Dieu-de-l-elec/AngstromIO-devboard/IMG/AIO demo.gif

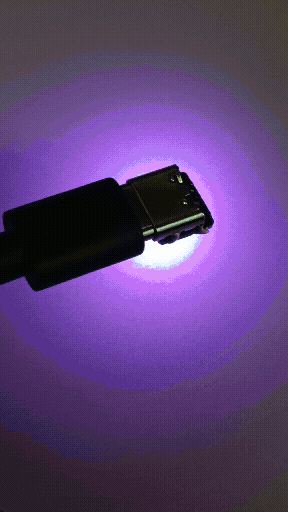
IMG/AIO demo.gif
