Dieu-de-l-elec/AngstromIO-devboard/IMG/angstromIO 3d S1.png

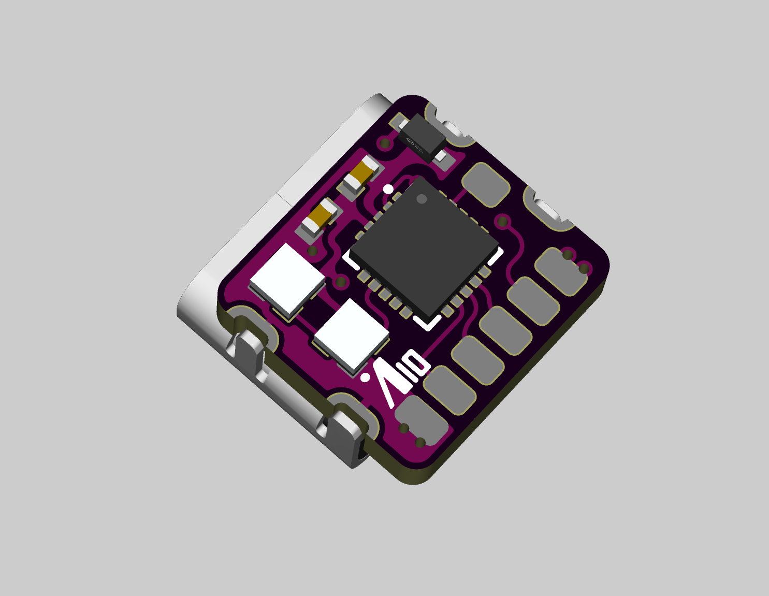
IMG/angstromIO 3d S1.png
