Dieu-de-l-elec/AngstromIO-devboard/IMG/angstromIO 3d S2.png

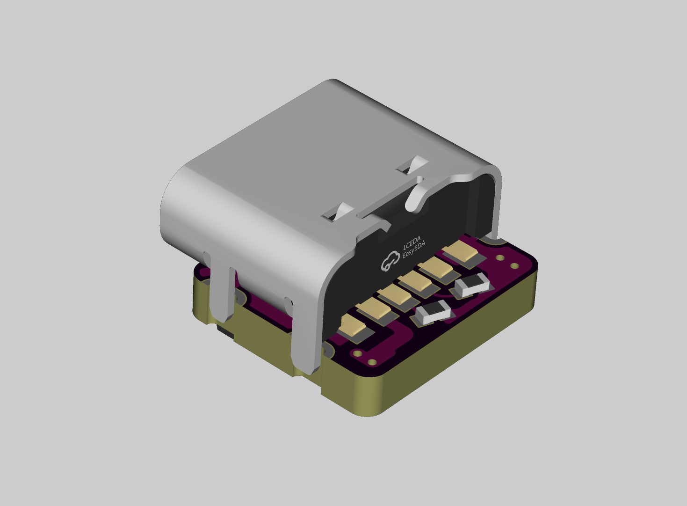
IMG/angstromIO 3d S2.png
