Dieu-de-l-elec/AngstromIO-devboard/IMG/angstromIO 3d S3.png

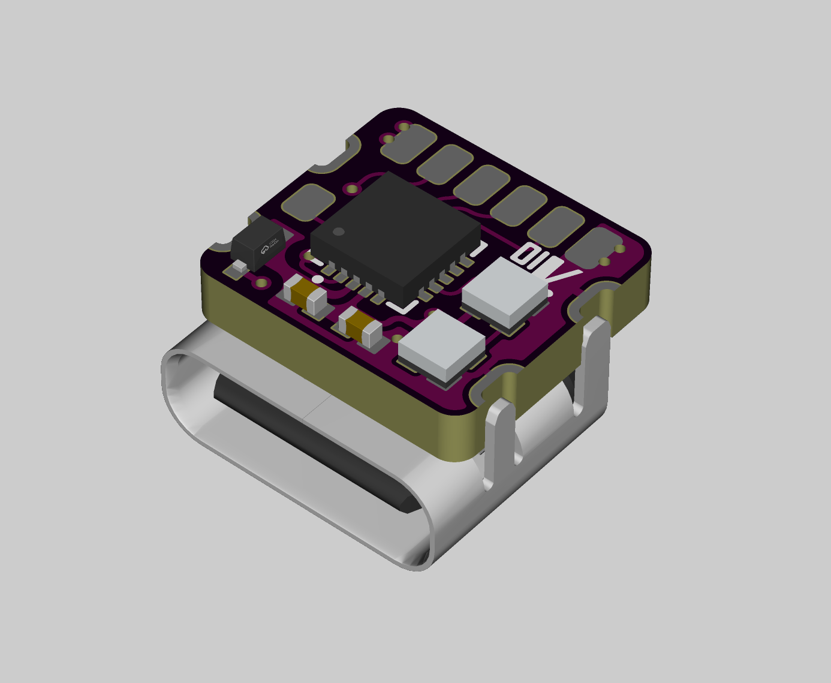
IMG/angstromIO 3d S3.png
