Dieu-de-l-elec/AngstromIO-devboard/IMG/angstromIO 3d S4.png

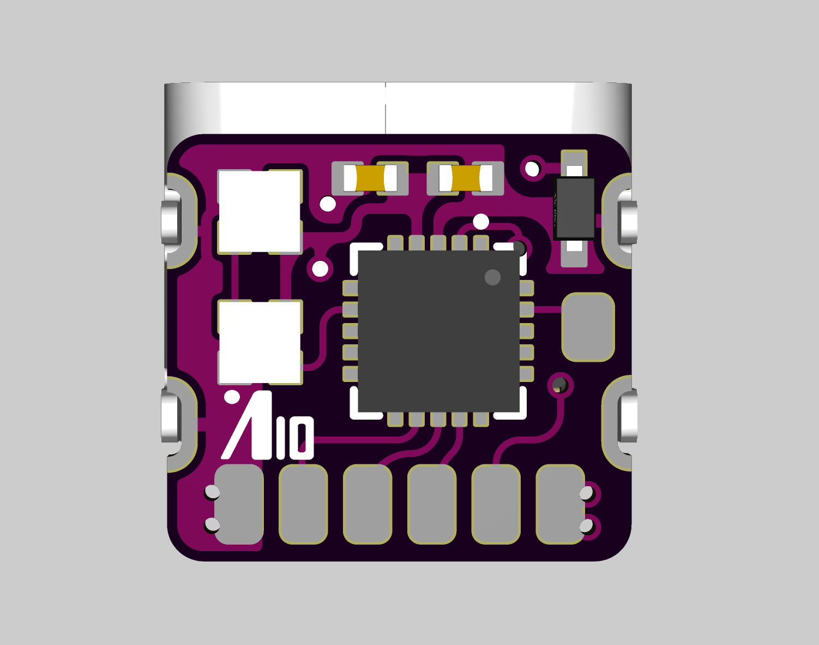
IMG/angstromIO 3d S4.png
