Dieu-de-l-elec/AngstromIO-devboard/IMG/angstromIO 3d S5.png

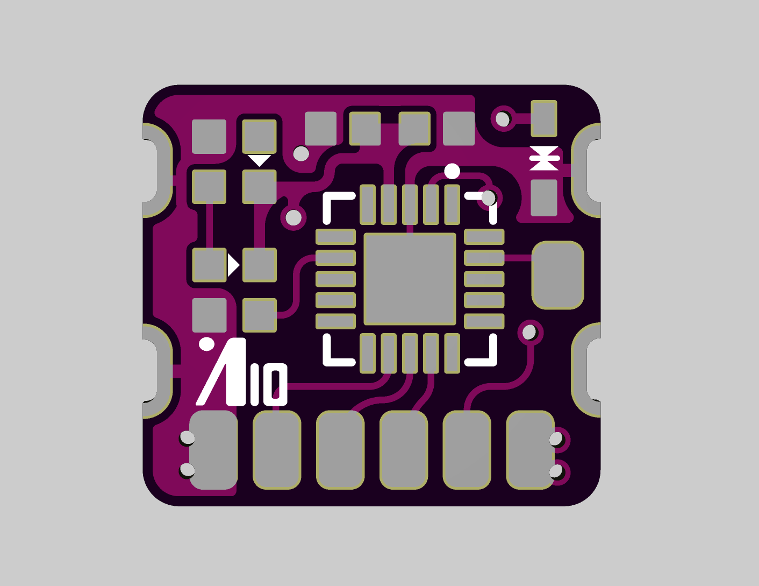
IMG/angstromIO 3d S5.png
