Dieu-de-l-elec/AngstromIO-devboard/IMG/angstromIO 3d S6.png

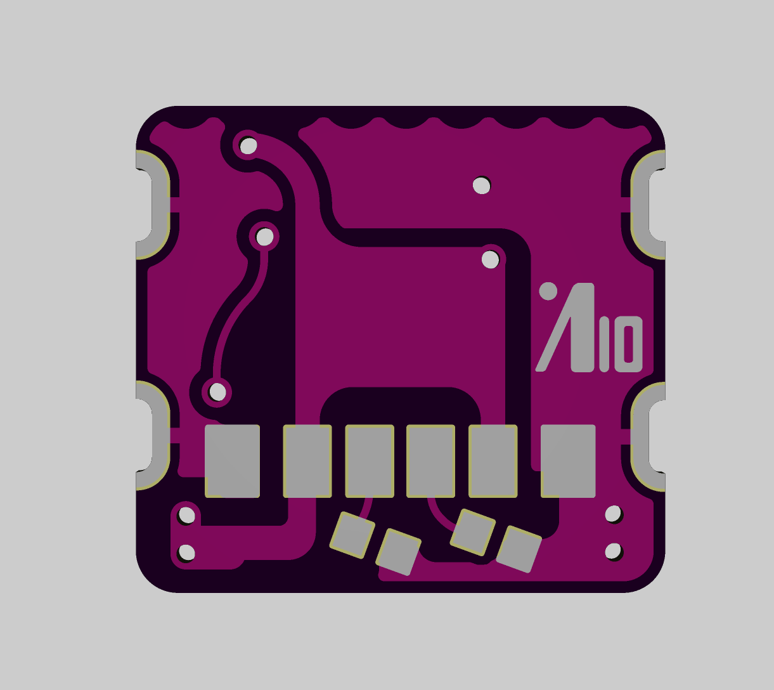
IMG/angstromIO 3d S6.png
