Dieu-de-l-elec/AngstromIO-devboard/IMG/CH32 Devboard 3D.png

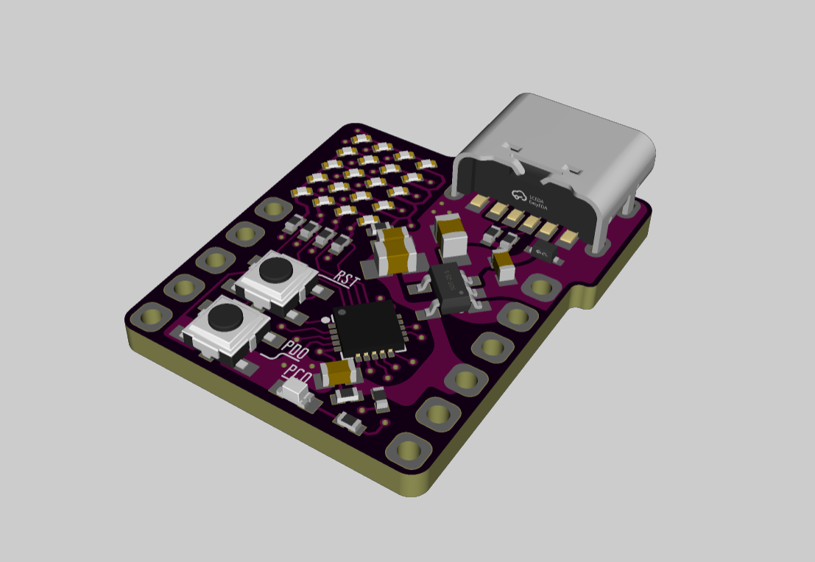
IMG/CH32 Devboard 3D.png
