Dieu-de-l-elec/AngstromIO-devboard/IMG/CH32 Devboard btm.png

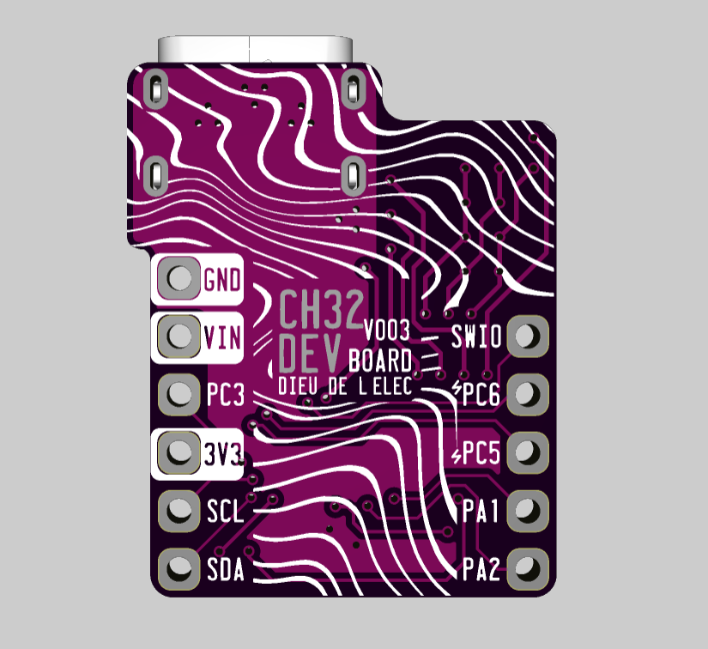
IMG/CH32 Devboard btm.png
