Dieu-de-l-elec/AngstromIO-devboard/IMG/CH32 Devboard top.png

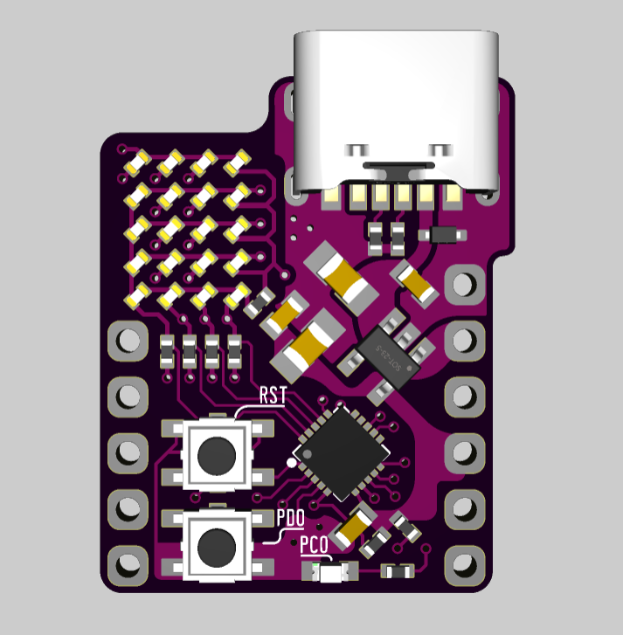
IMG/CH32 Devboard top.png
