Dieu-de-l-elec/AngstromIO-devboard/IMG/Global.jpg

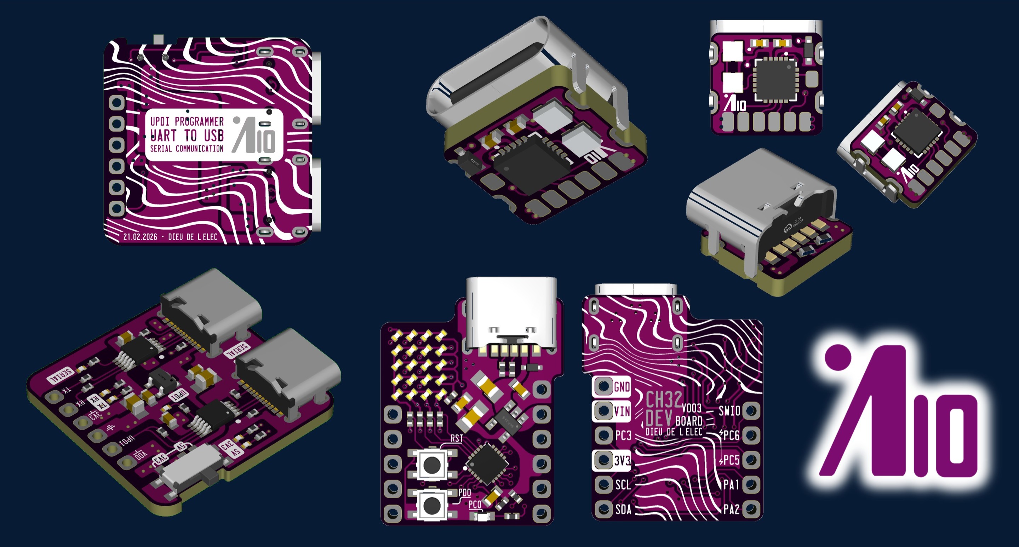
IMG/Global.jpg
