Dieu-de-l-elec/AngstromIO-devboard/IMG/Layout bottom AIO clean.png

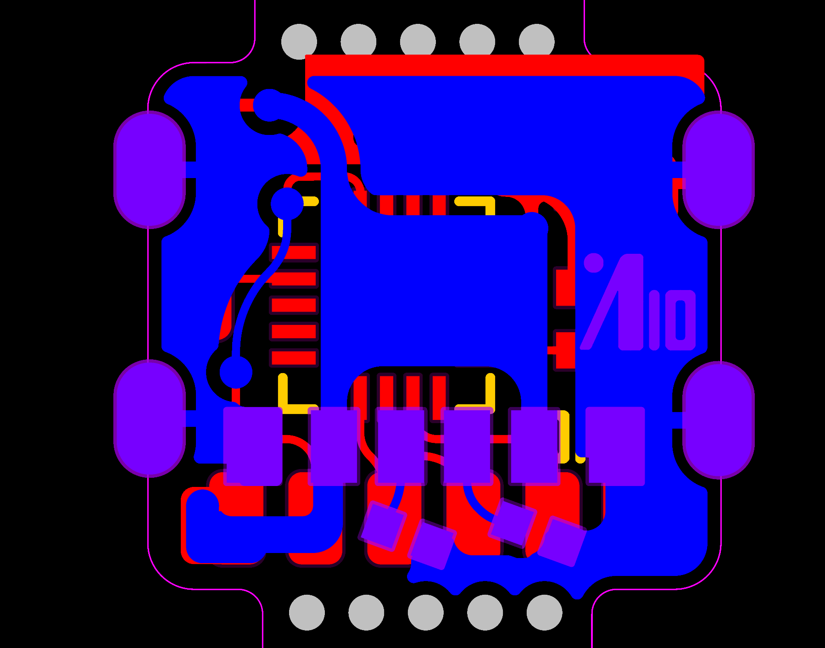
IMG/Layout bottom AIO clean.png
