Dieu-de-l-elec/AngstromIO-devboard/IMG/Layout bottom AIO.png

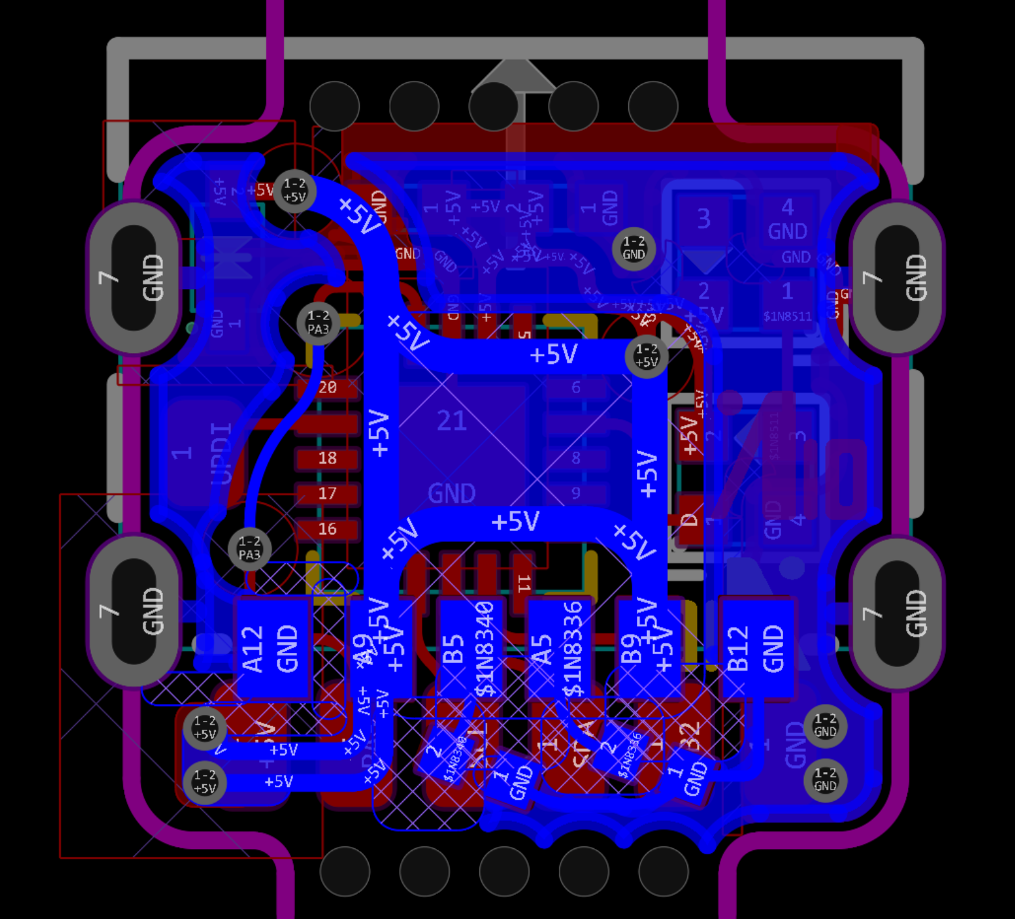
IMG/Layout bottom AIO.png
