Dieu-de-l-elec/AngstromIO-devboard/IMG/Layout bottom CH32 devboard clean.png

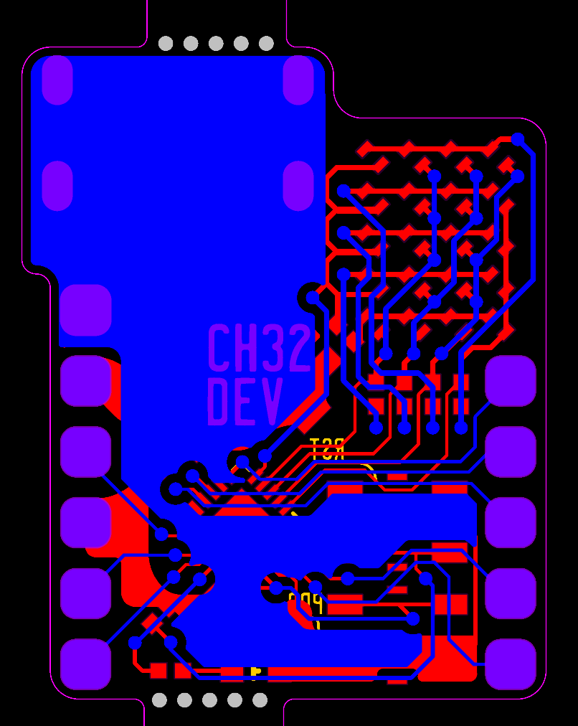
IMG/Layout bottom CH32 devboard clean.png
