Dieu-de-l-elec/AngstromIO-devboard/IMG/Layout bottom CH32 devboard.png

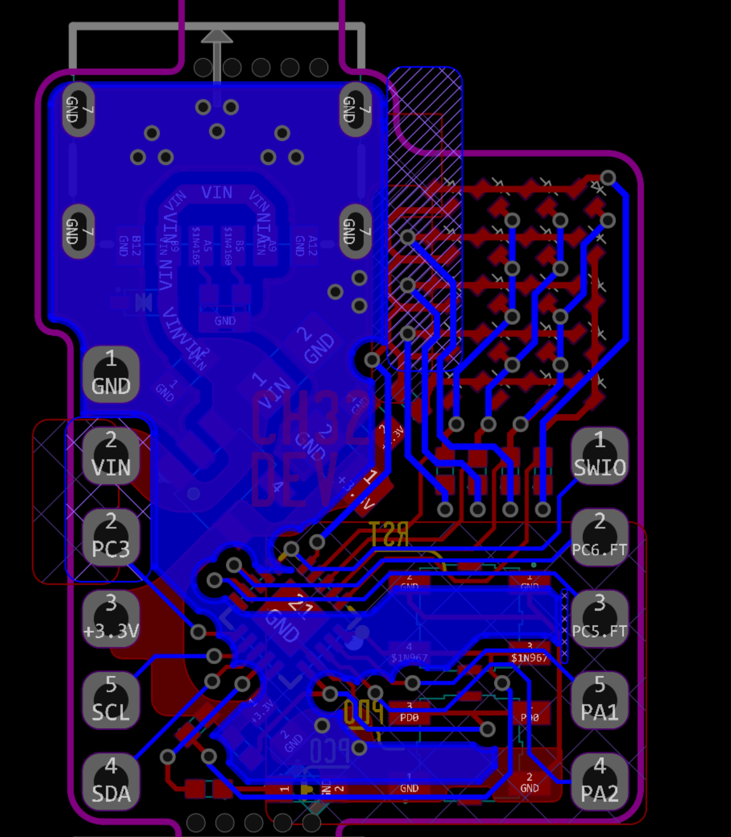
IMG/Layout bottom CH32 devboard.png
