Dieu-de-l-elec/AngstromIO-devboard/IMG/Layout bottom panel.png

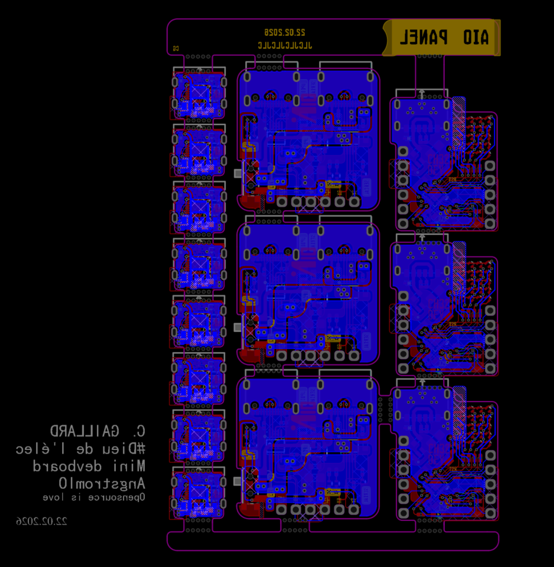
IMG/Layout bottom panel.png
