Dieu-de-l-elec/AngstromIO-devboard/IMG/Layout bottom programmer clean.png

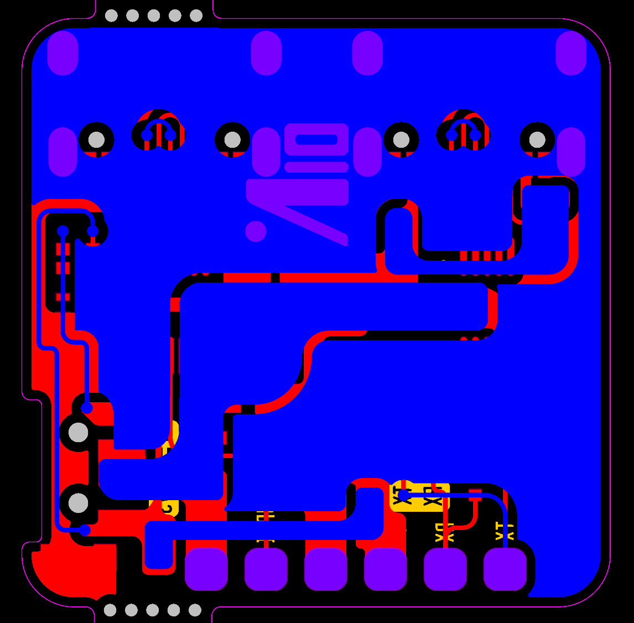
IMG/Layout bottom programmer clean.png
