Dieu-de-l-elec/AngstromIO-devboard/IMG/Layout bottom programmer.png

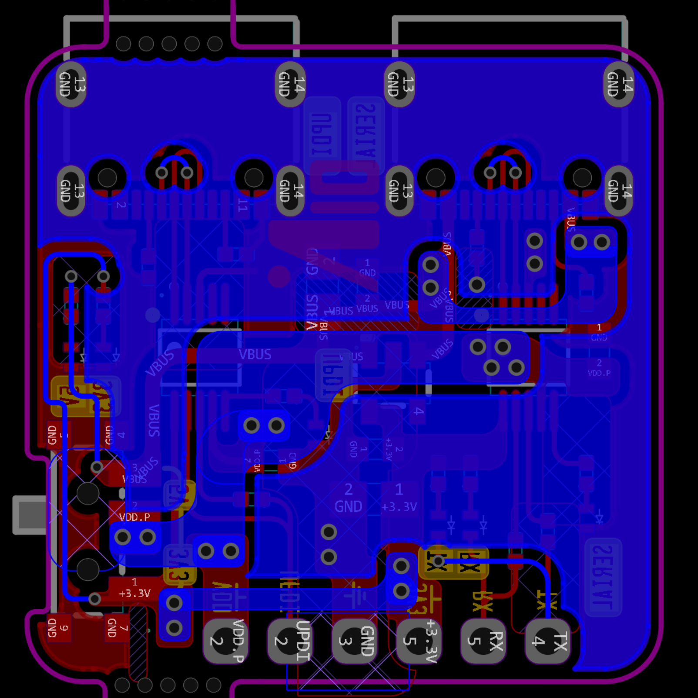
IMG/Layout bottom programmer.png
