Dieu-de-l-elec/AngstromIO-devboard/IMG/Layout top AIO clean.png

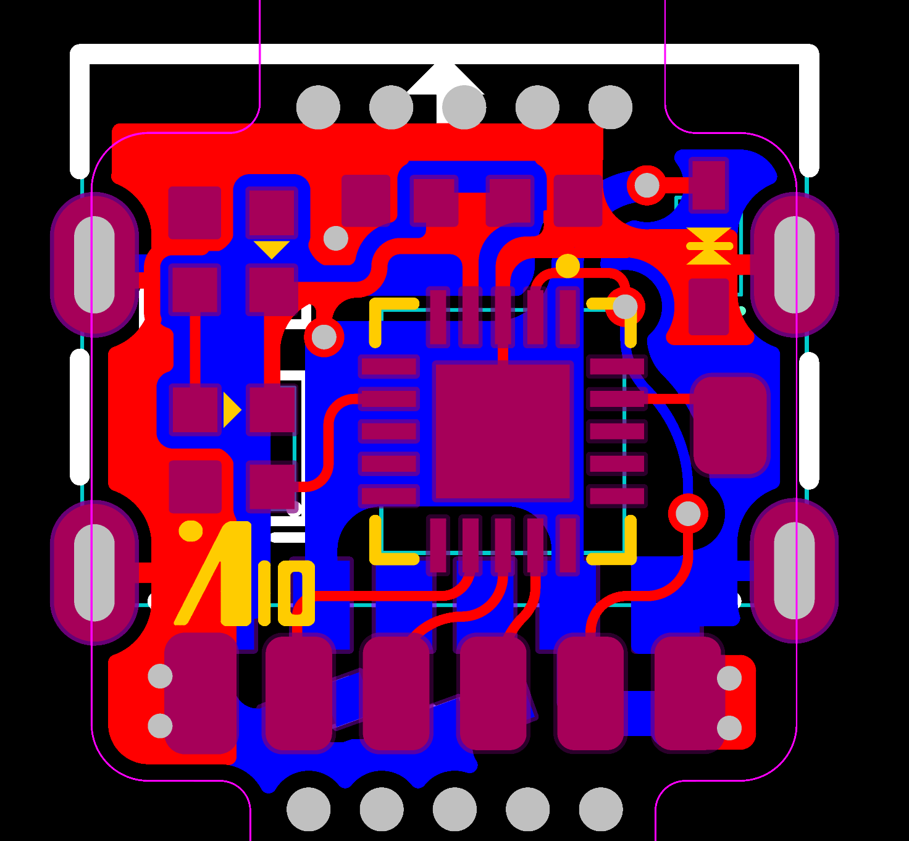
IMG/Layout top AIO clean.png
