Dieu-de-l-elec/AngstromIO-devboard/IMG/Layout top AIO.png

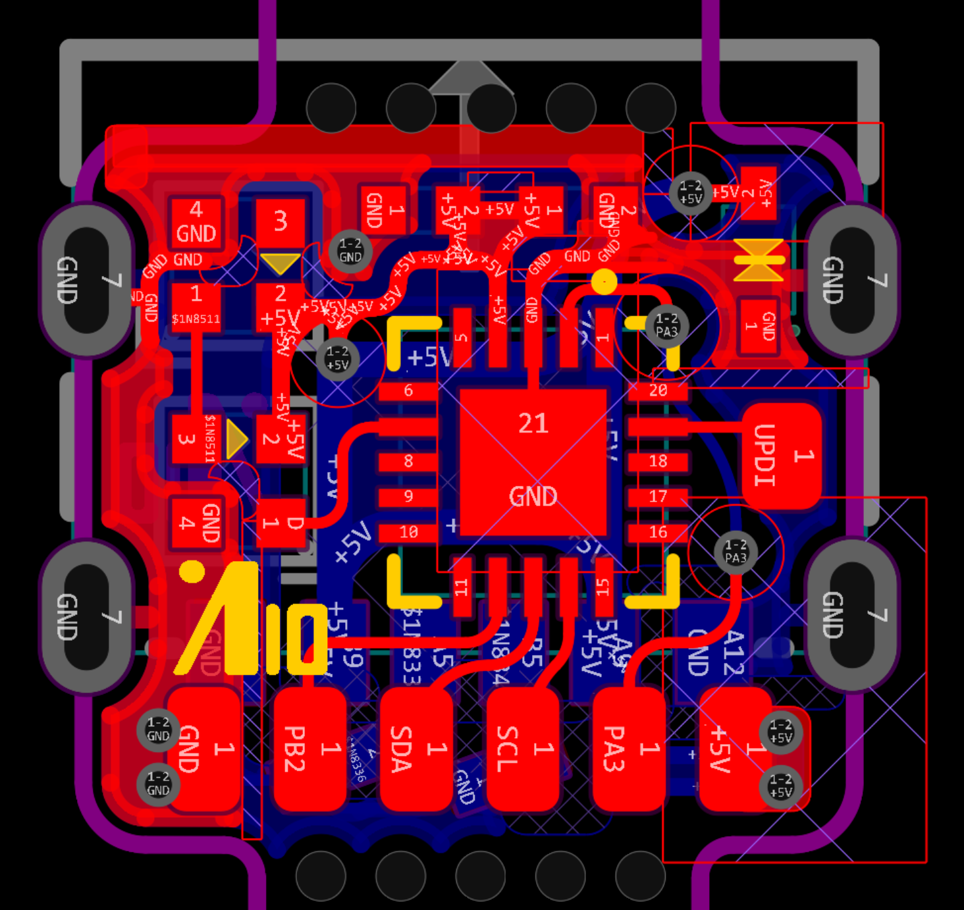
IMG/Layout top AIO.png
