Dieu-de-l-elec/AngstromIO-devboard/IMG/Layout top CH32 devboard clean.png

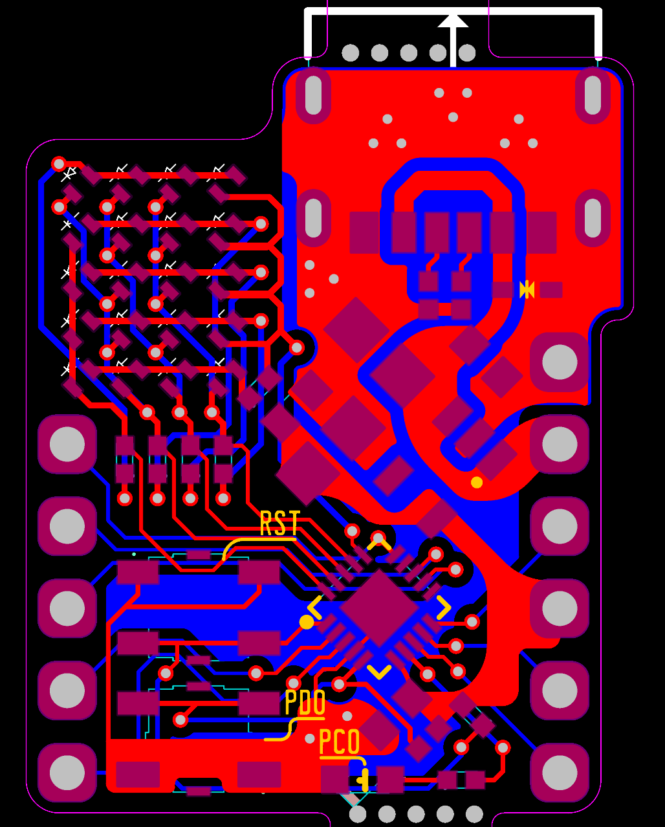
IMG/Layout top CH32 devboard clean.png
