Dieu-de-l-elec/AngstromIO-devboard/IMG/Layout top CH32 devboard.png

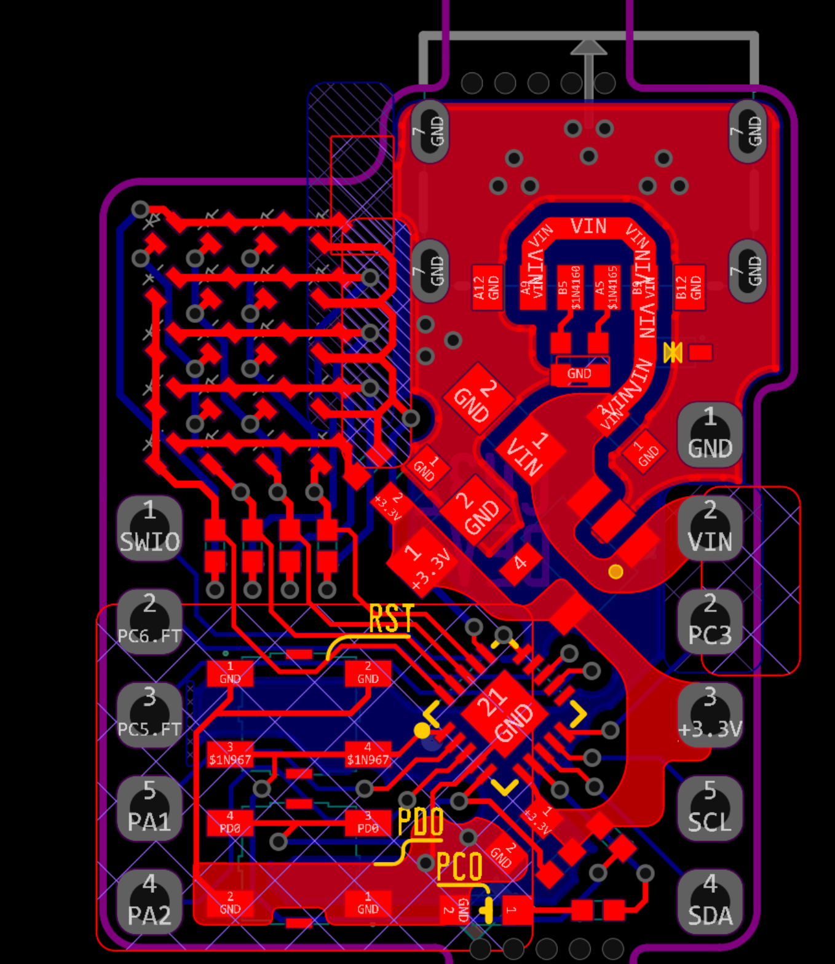
IMG/Layout top CH32 devboard.png
