Dieu-de-l-elec/AngstromIO-devboard/IMG/Layout top panel.png

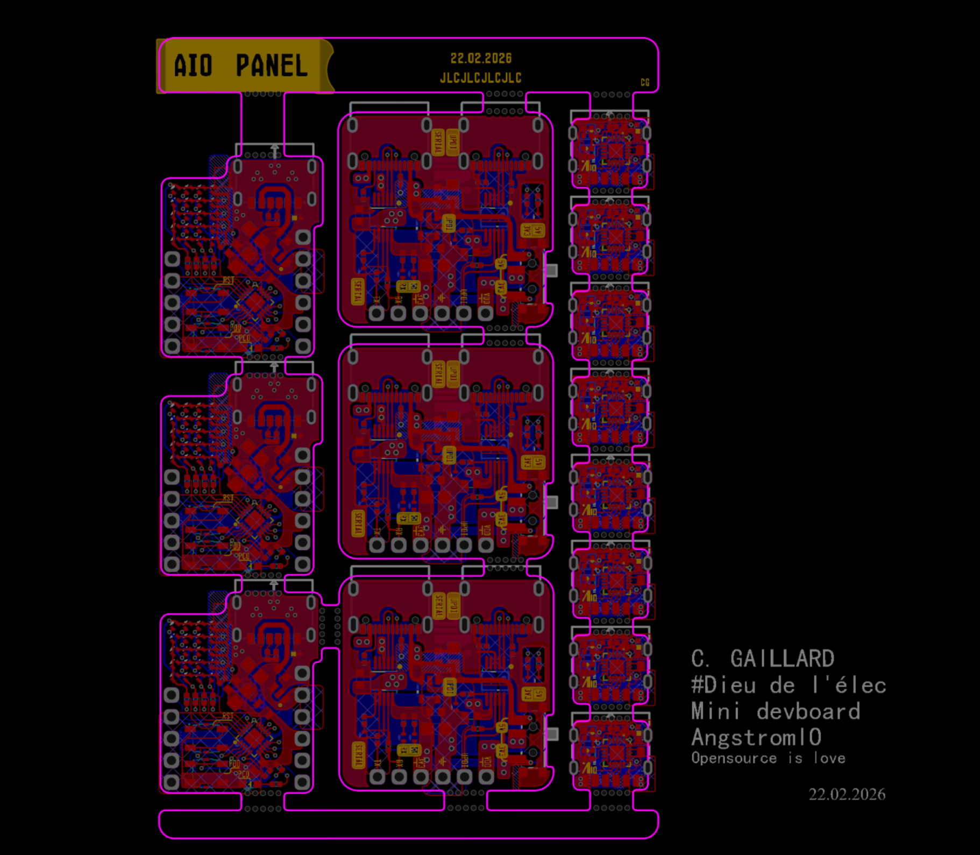
IMG/Layout top panel.png
