Dieu-de-l-elec/AngstromIO-devboard/IMG/Layout top programmer clean.png

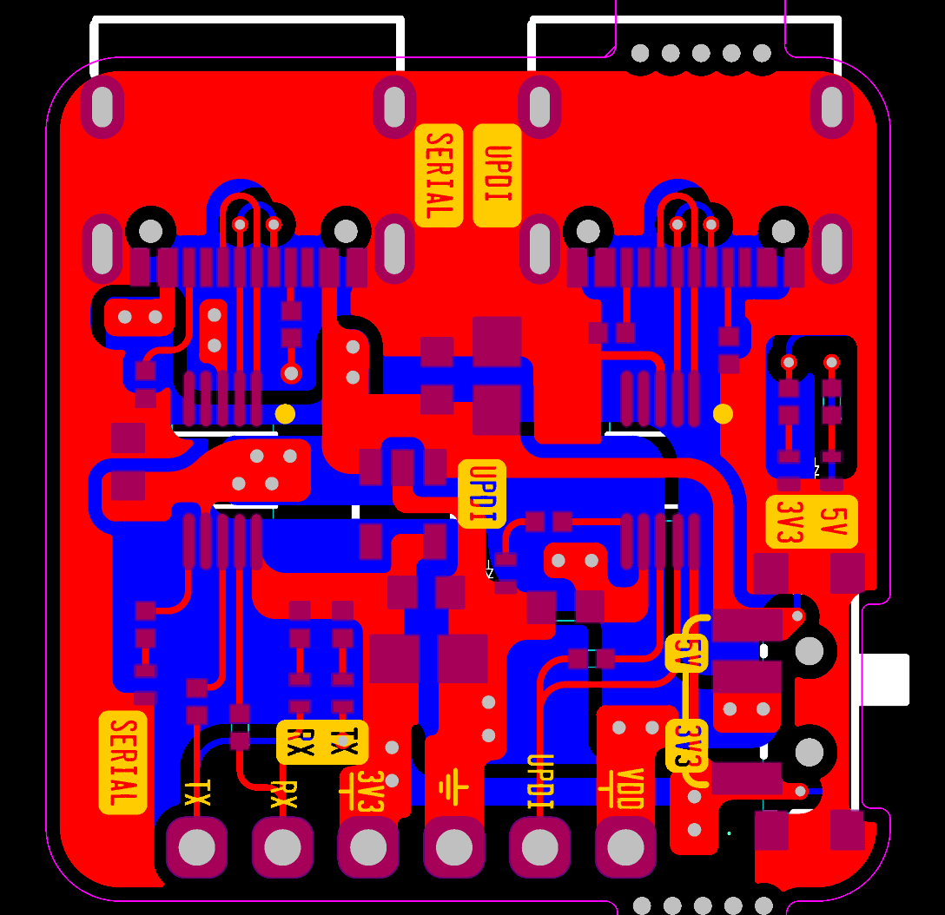
IMG/Layout top programmer clean.png
