Dieu-de-l-elec/AngstromIO-devboard/IMG/Layout top programmer.png

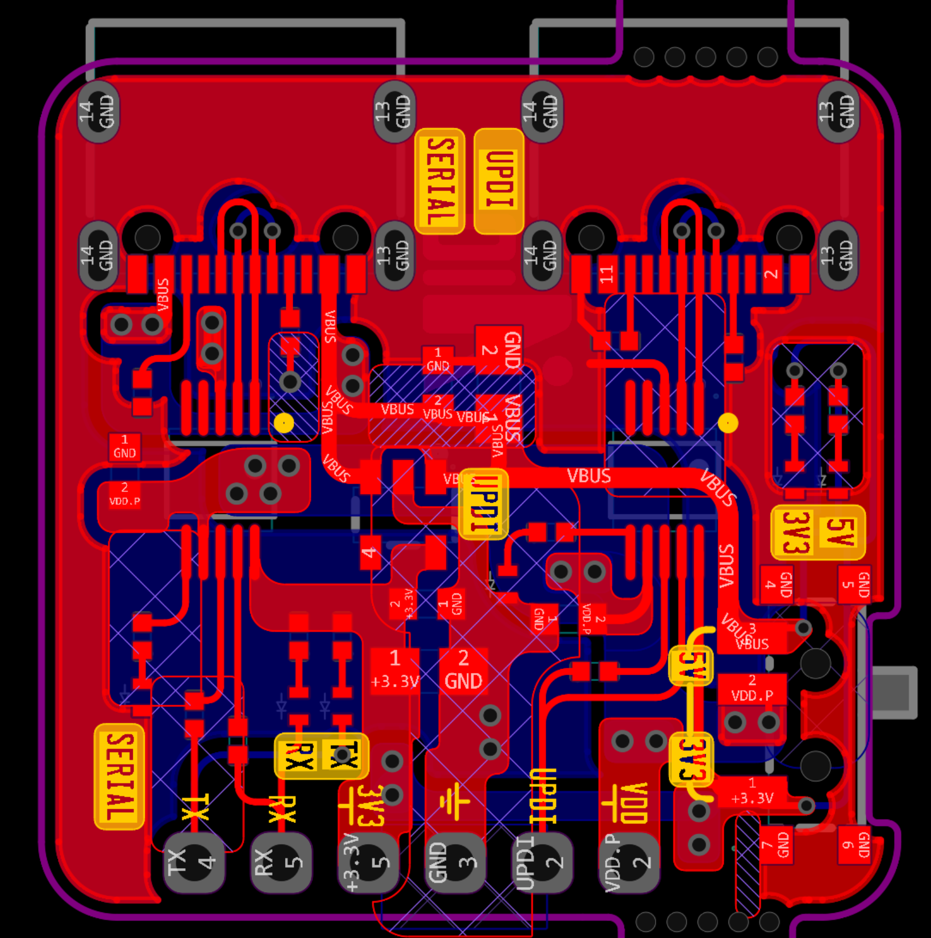
IMG/Layout top programmer.png
