Dieu-de-l-elec/AngstromIO-devboard/IMG/Programmer PCB 2D.jpg

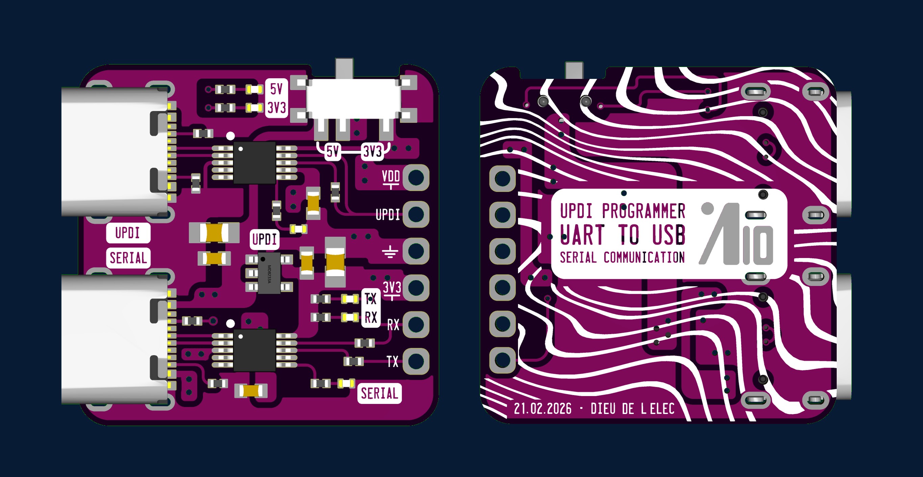
IMG/Programmer PCB 2D.jpg
