Dieu-de-l-elec/AngstromIO-devboard/IMG/Programmer PCB 3D.jpg

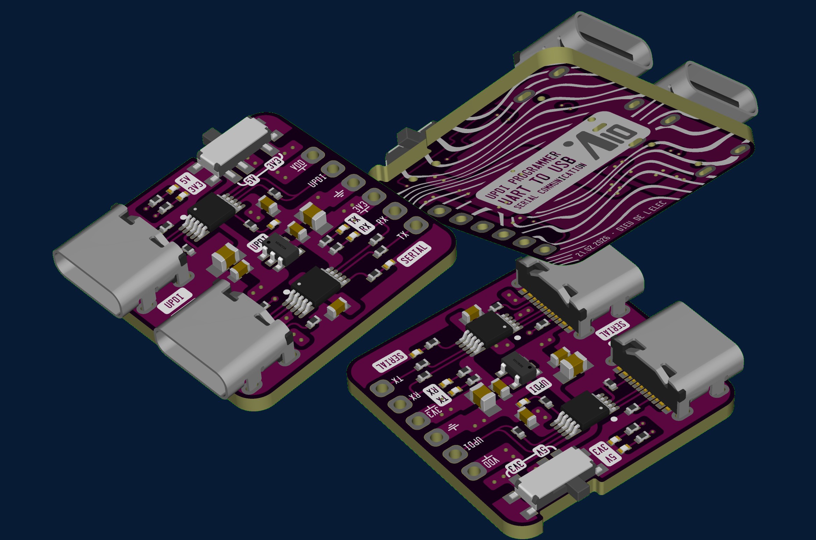
IMG/Programmer PCB 3D.jpg
