Dieu-de-l-elec/AngstromIO-devboard/IMG/RENDERS/AIO/001.png

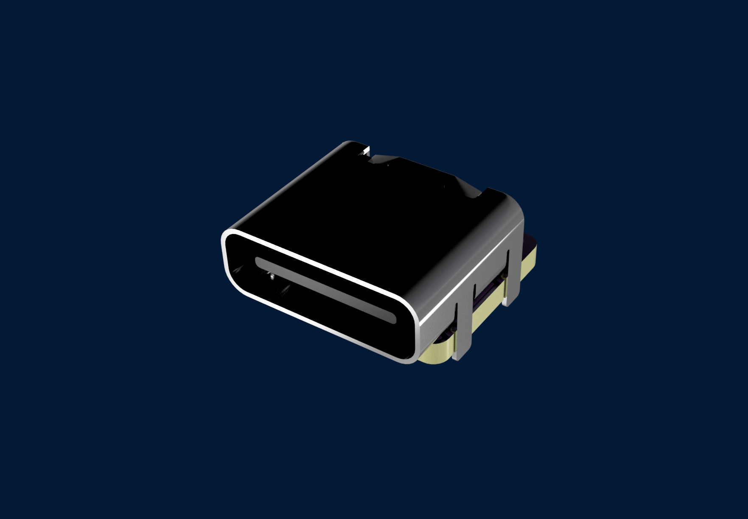
IMG/RENDERS/AIO/001.png
