Dieu-de-l-elec/AngstromIO-devboard/IMG/RENDERS/AIO/002.png

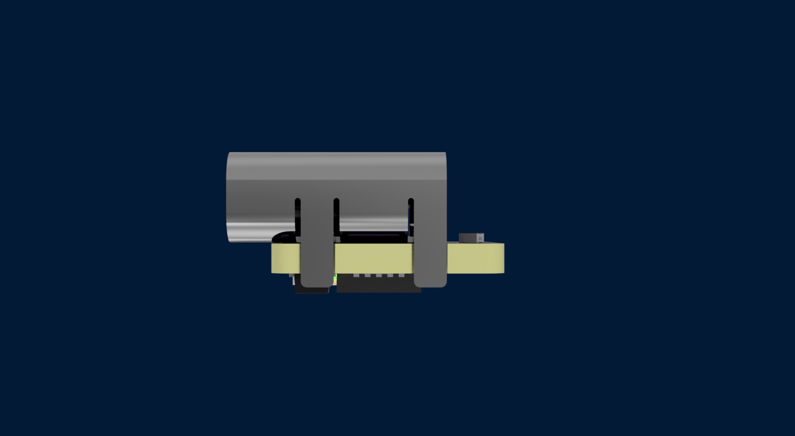
IMG/RENDERS/AIO/002.png
