Dieu-de-l-elec/AngstromIO-devboard/IMG/RENDERS/AIO/003.png

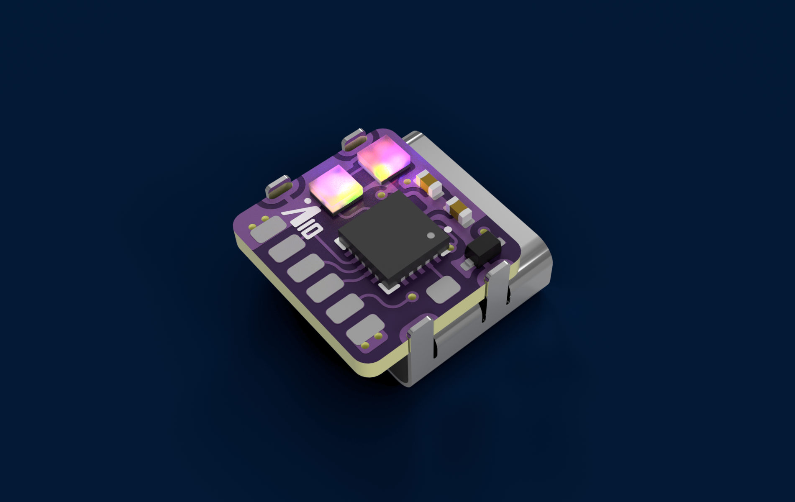
IMG/RENDERS/AIO/003.png
