Dieu-de-l-elec/AngstromIO-devboard/IMG/RENDERS/AIO/004.png

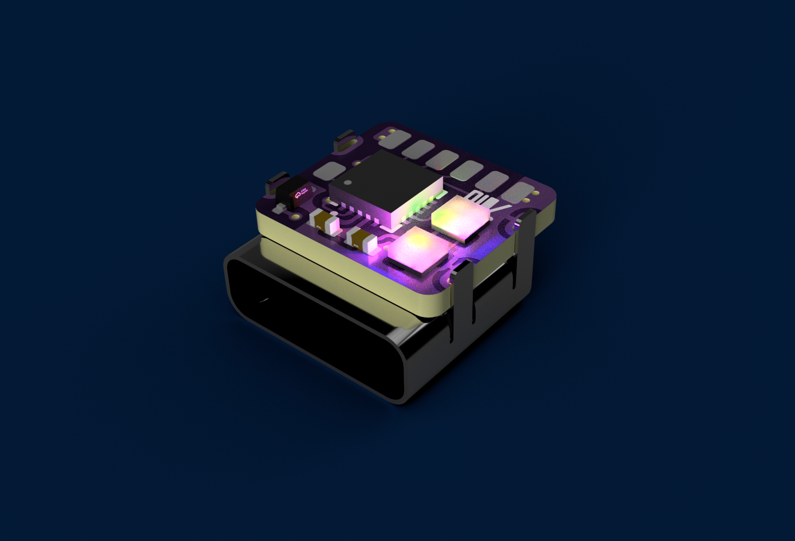
IMG/RENDERS/AIO/004.png
