Dieu-de-l-elec/AngstromIO-devboard/IMG/RENDERS/AIO/005.png

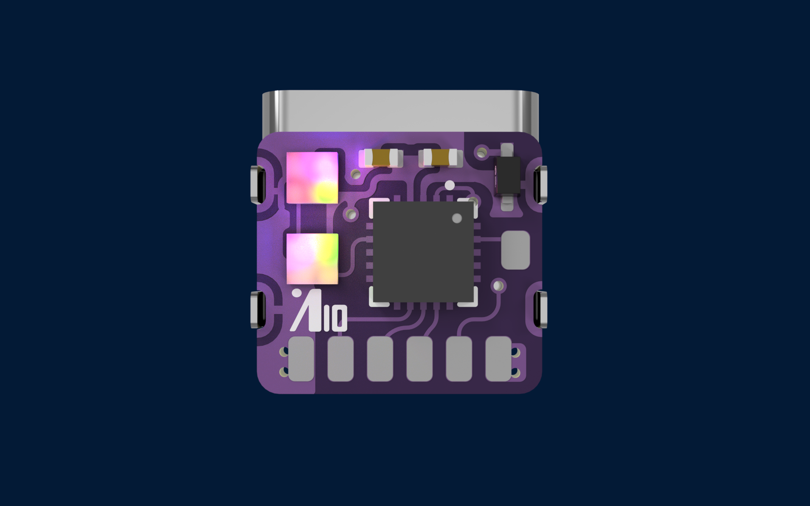
IMG/RENDERS/AIO/005.png
