Dieu-de-l-elec/AngstromIO-devboard/IMG/RENDERS/AIO/006.png

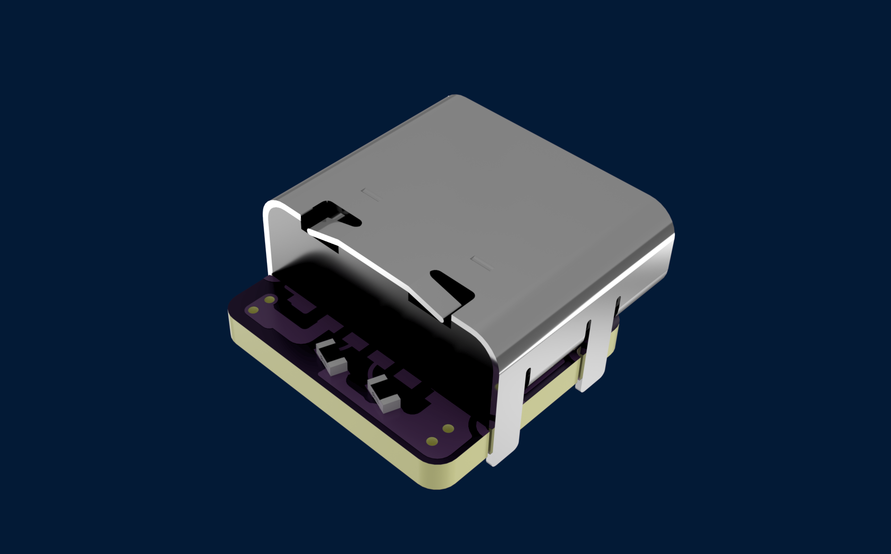
IMG/RENDERS/AIO/006.png
