Dieu-de-l-elec/AngstromIO-devboard/IMG/RENDERS/AIO/007.png

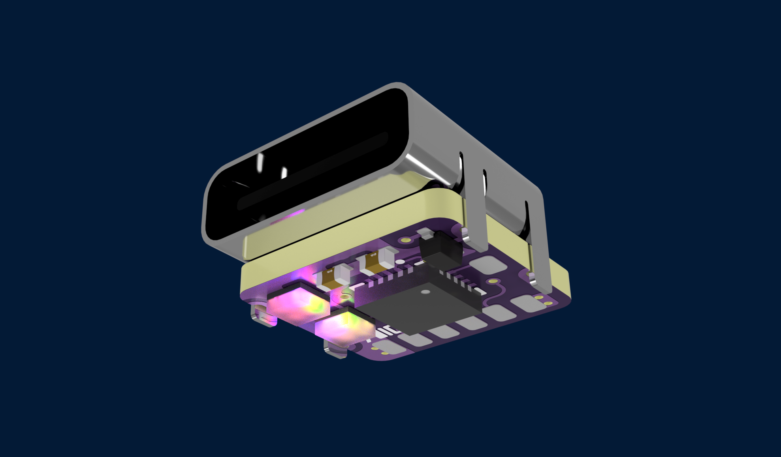
IMG/RENDERS/AIO/007.png
