Dieu-de-l-elec/AngstromIO-devboard/IMG/BUILD/size comparison.jpg

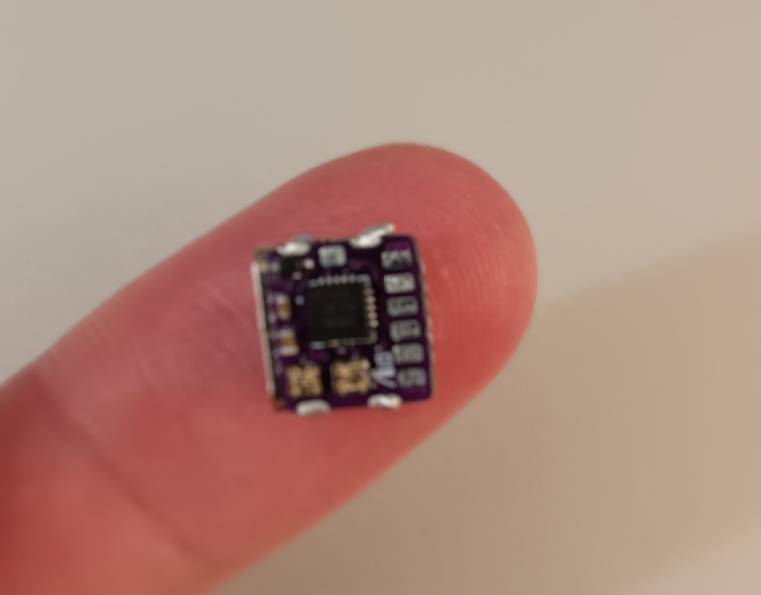
IMG/BUILD/size comparison.jpg
